Apollo917/skilleton/materials/all-components.png

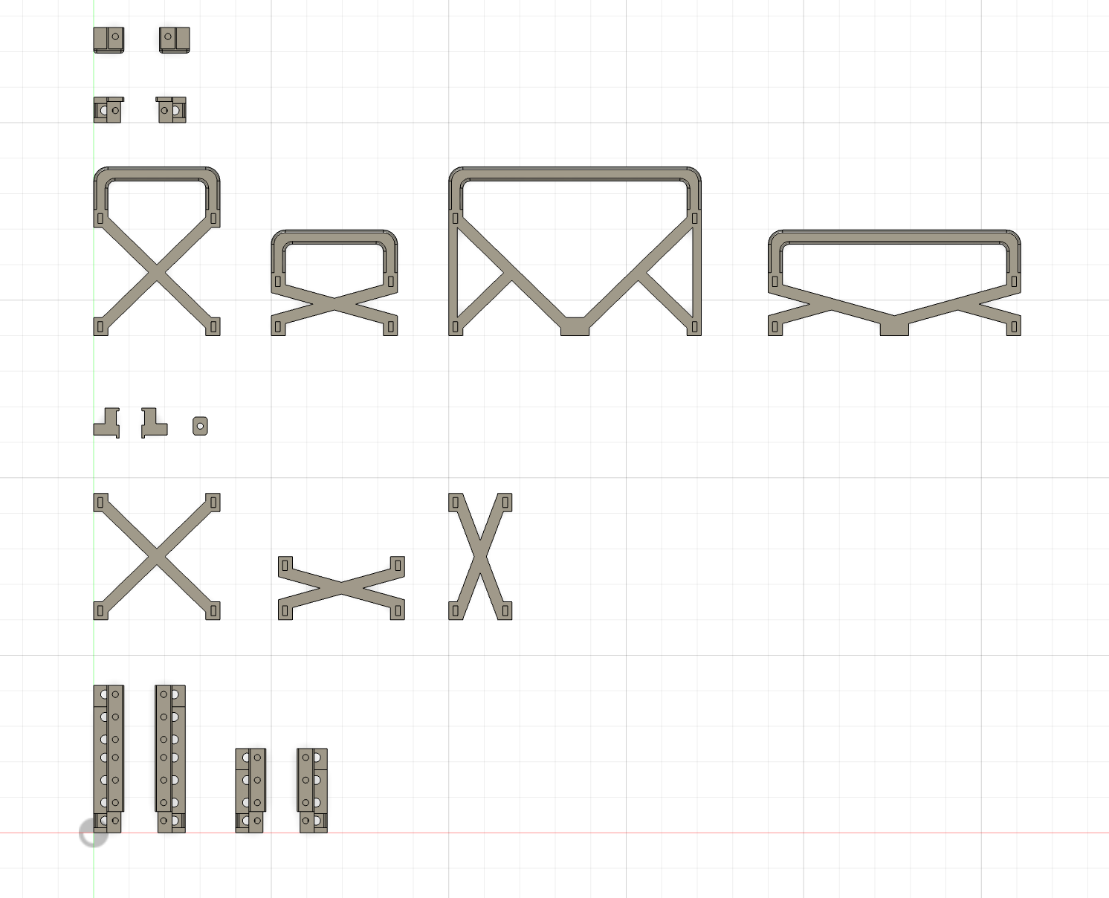
materials/all-components.png
