Apollo917/skilleton/materials/preview-3-4.png

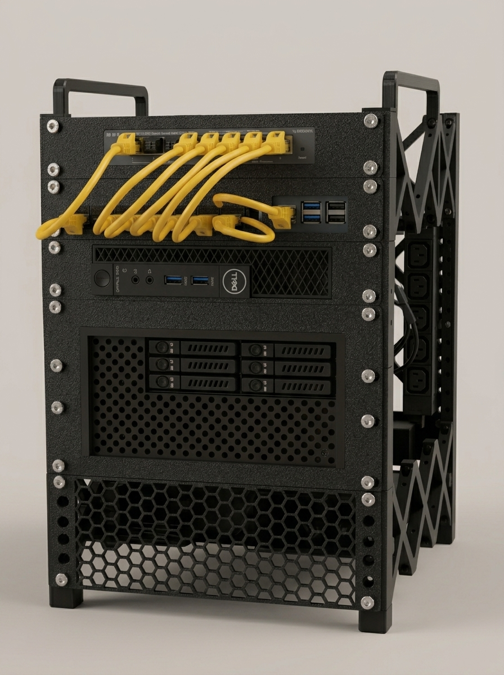
materials/preview-3-4.png
